xhusar2/night_vision_devices-thermal_monocular/resources/wiring/thermal_monocular.kicad_sch

## KiCad design resources/wiring/thermal_monocular.kicad_sch (2026-01-22)

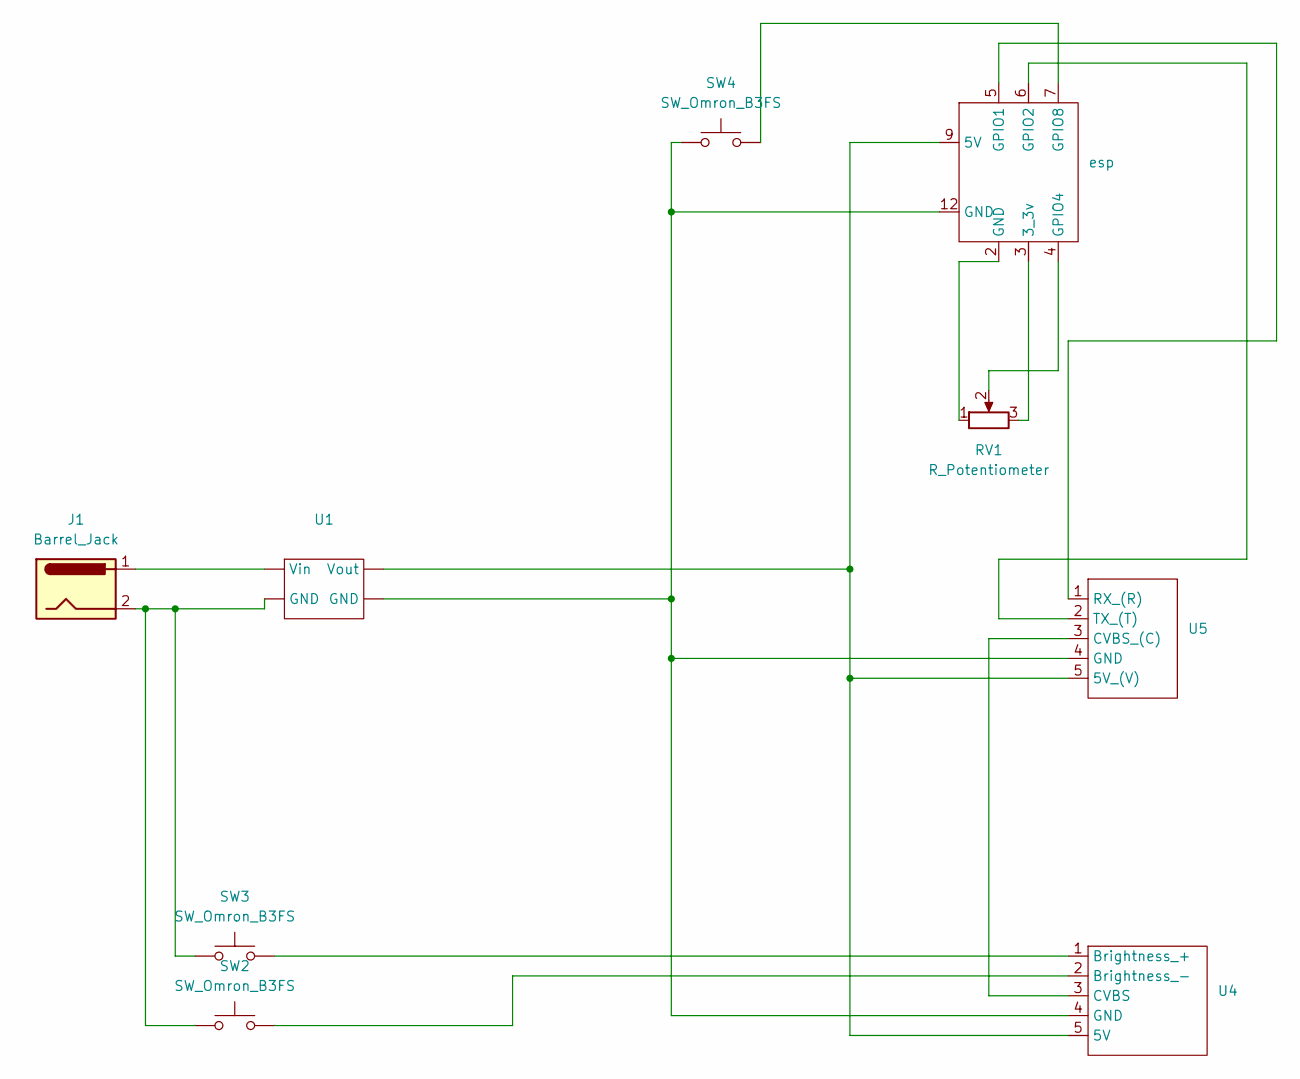
[picture p7: schematic thermal_monocular.kicad_sch]

Parts:
J1: Barrel_Jack
RV1: R_Potentiometer
SW2, SW3, SW4: SW_Omron_B3FS
U1, U4, U5: (no value)
esp: (no value)

Connections:
unnamed: J1.1, U1.
unnamed: J1.2, SW2.1, SW3.1, U1.
unnamed: RV1.1, esp.2 (GND)
unnamed: RV1.2, esp.4 (GPIO4)
unnamed: RV1.3, esp.3 (3_3v)
unnamed: SW2.2, U4.2 (Brightness_-)
unnamed: SW3.2, U4.1 (Brightness_+)
unnamed: SW4.1, U1., U4.4 (GND), U5.4 (GND), esp.12 (GND)
unnamed: SW4.2, esp.7 (GPIO8)
unnamed: U1., U4.5 (5V), U5.5 (5V_(V)), esp.9 (5V)
unnamed: U4.3 (CVBS), U5.3 (CVBS_(C))
unnamed: U5.1 (RX_(R)), esp.5 (GPIO1)
unnamed: U5.2 (TX_(T)), esp.6 (GPIO2)
